WindsorHSRobotics/team-5115_2017-18/prints/gears/soldworks or fussion files/pinion rack mk1.SLDPRT

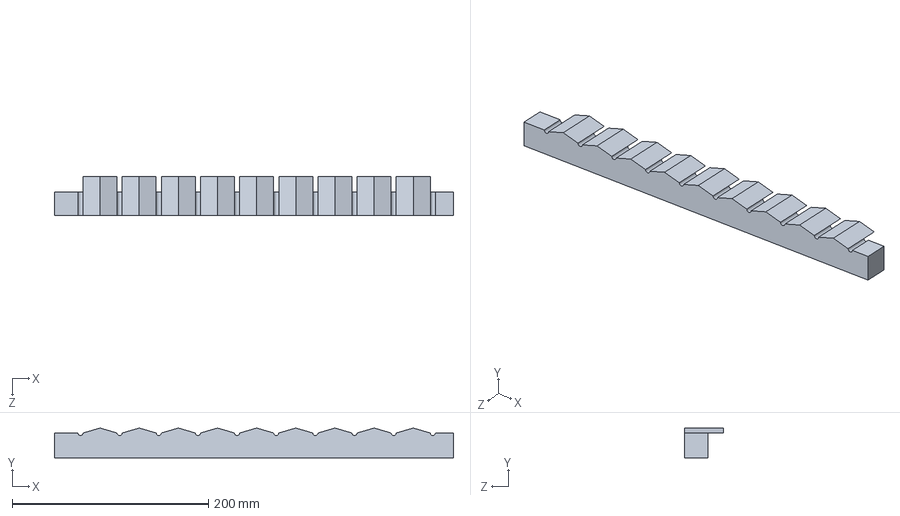
[picture p18: CAD file, 2018-01-17]
prints/gears/soldworks or fussion files/pinion rack mk1.SLDPRT
406.4 x 30.5 x 39.6 mm
