WindsorHSRobotics/team-5115_2017-18/prints/8020 brackets/stl files/90 degree 3 way corner bracket.stl

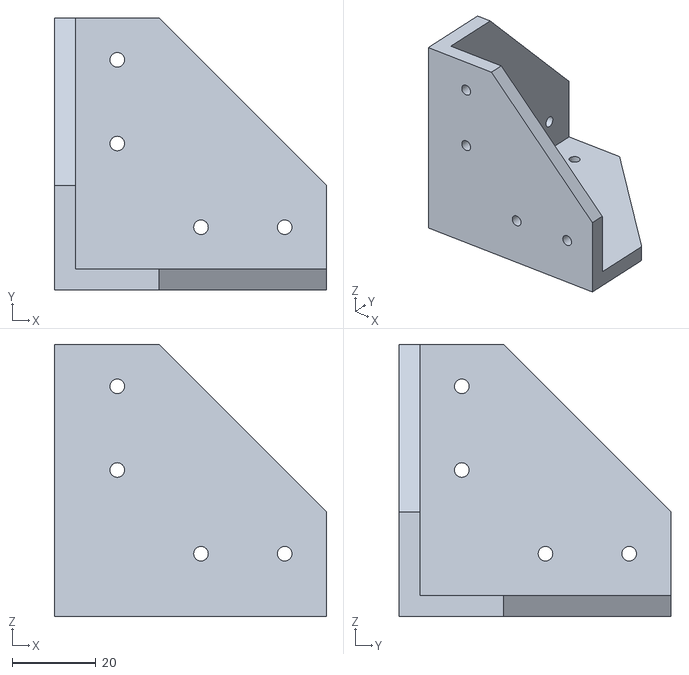
[picture p19: CAD file, 2017-10-06]
prints/8020 brackets/stl files/90 degree 3 way corner bracket.stl
65.0 x 65.0 x 65.0
