WindsorHSRobotics/team-5115_2017-18/prints/adapters/stl files/clawmk5.STL

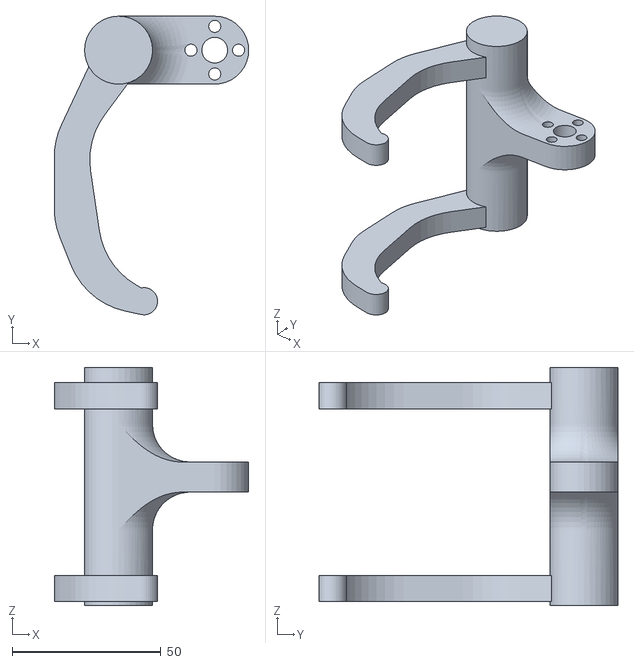
[picture p20: CAD file, 2018-01-09]
prints/adapters/stl files/clawmk5.STL
65.4 x 100.4 x 80.0
