WindsorHSRobotics/team-5115_2017-18/prints/gears/soldworks or fussion files/pin mk1.SLDPRT

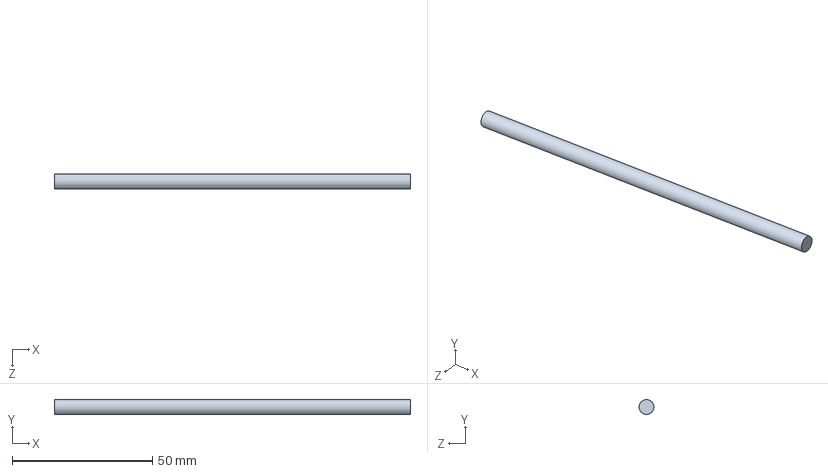
[picture p22: CAD file, 2018-01-17]
prints/gears/soldworks or fussion files/pin mk1.SLDPRT
127.0 x 5.33 x 5.33 mm
