WindsorHSRobotics/team-5115_2017-18/prints/gears/stl files/Gear_Rack_4inCircumference_2.222inLength.stl

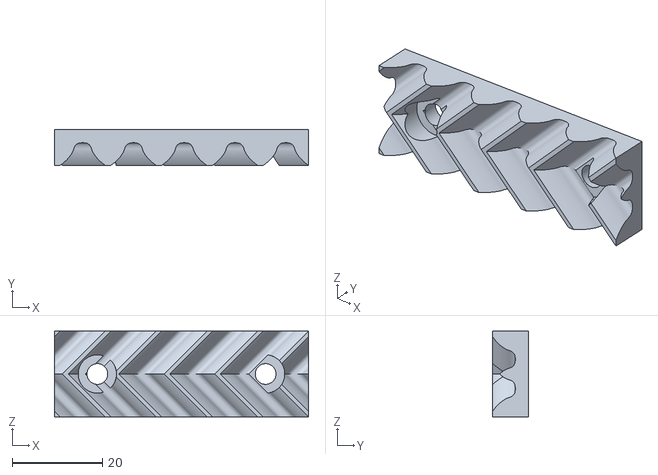
[picture p23: CAD file, 2017-12-08]
prints/gears/stl files/Gear_Rack_4inCircumference_2.222inLength.stl
56.4 x 7.94 x 19.1
