WindsorHSRobotics/team-5115_2017-18/prints/8020 brackets/stl files/90 degree joining plane.stl

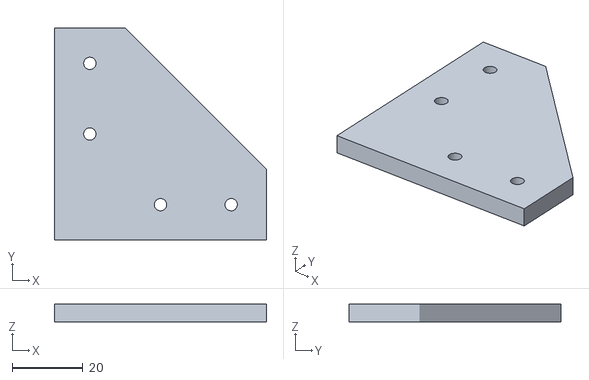
[picture p24: CAD file, 2017-10-06]
prints/8020 brackets/stl files/90 degree joining plane.stl
60.0 x 60.0 x 5.00
