WindsorHSRobotics/team-5115_2017-18/prints/adapters/sketchup of fusion files/4in mechanum adapter.SLDPRT

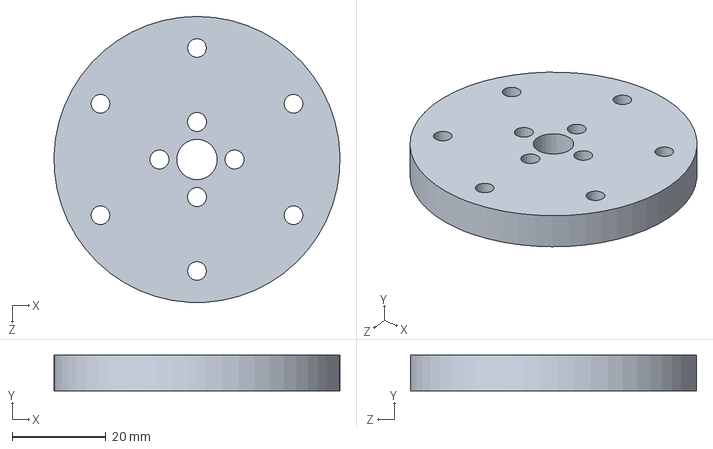
[picture p25: CAD file, 2018-01-30]
prints/adapters/sketchup of fusion files/4in mechanum adapter.SLDPRT
60.9 x 7.62 x 61.0 mm
