WindsorHSRobotics/team-5115_2017-18/prints/adapters/stl files/core device strain relief 1.STL

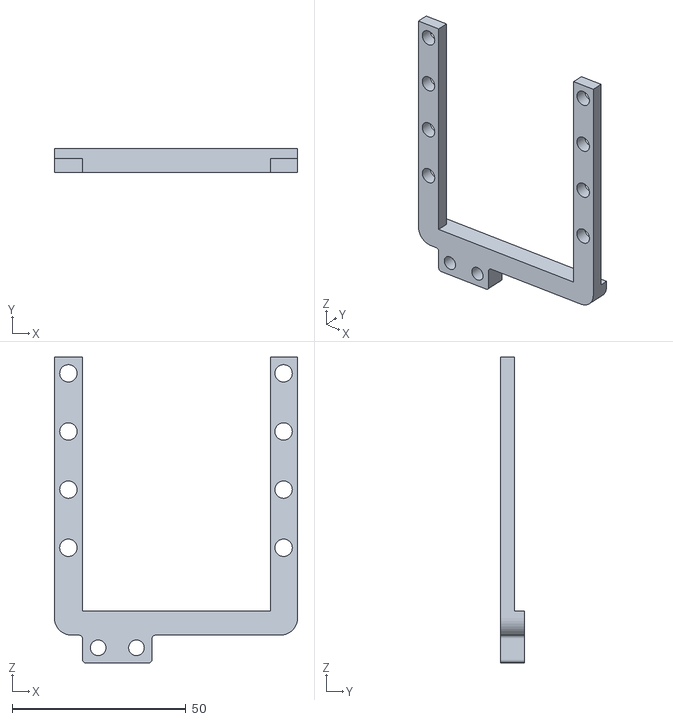
[picture p26: CAD file, 2017-12-21]
prints/adapters/stl files/core device strain relief 1.STL
70.0 x 6.80 x 88.0
