WindsorHSRobotics/team-5115_2017-18/prints/connectors/hinges/sti files/hinge pin.stl

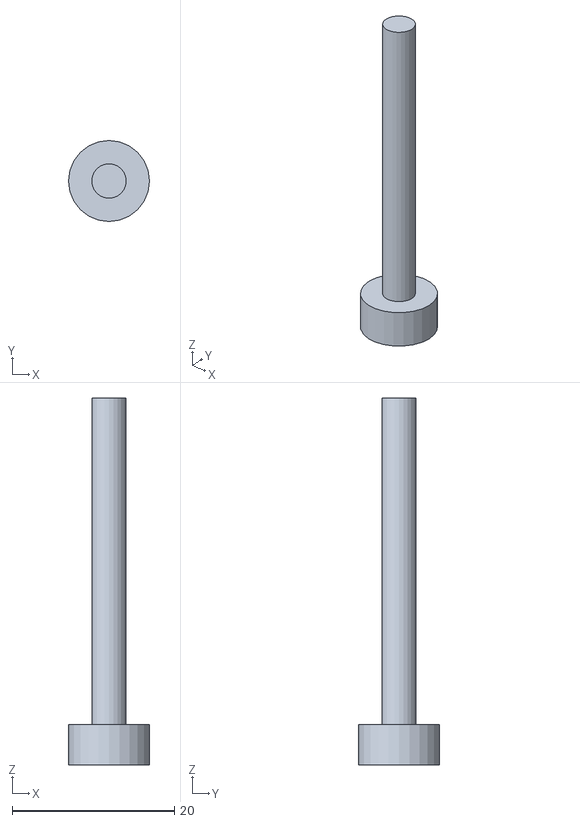
[picture p27: CAD file, 2017-10-03]
prints/connectors/hinges/sti files/hinge pin.stl
10.0 x 10.0 x 45.3
