WindsorHSRobotics/team-5115_2017-18/prints/gears/stl files/GearPinion_4inCircumference.stl

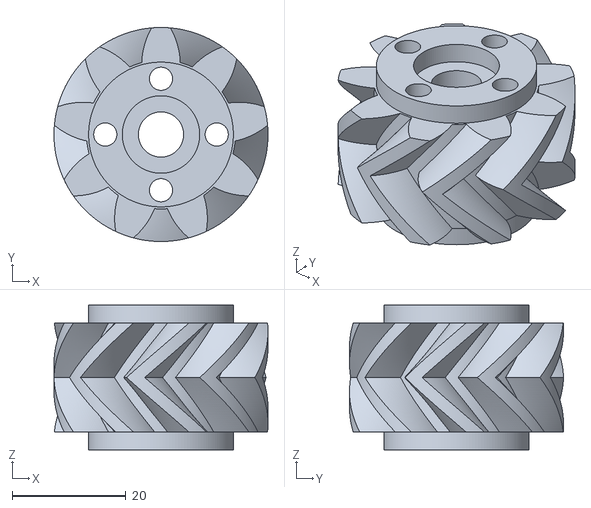
[picture p28: CAD file, 2017-12-08]
prints/gears/stl files/GearPinion_4inCircumference.stl
37.5 x 37.5 x 25.4
