WindsorHSRobotics/team-5115_2017-18/prints/8020 brackets/stl files/t joining plate.stl

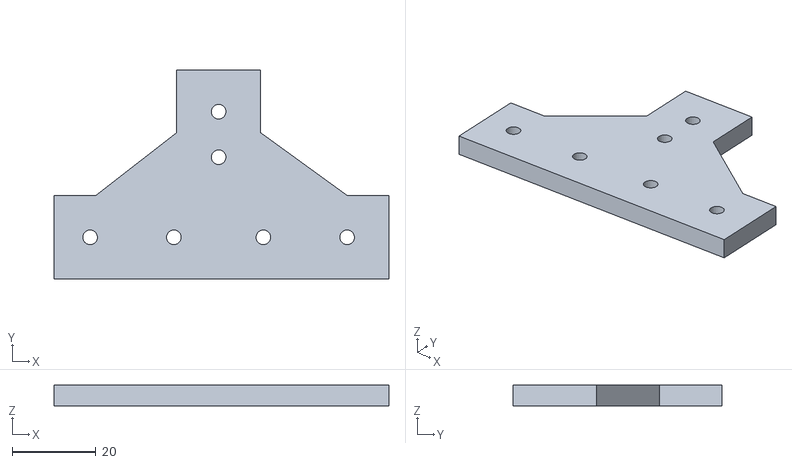
[picture p29: CAD file, 2017-10-06]
prints/8020 brackets/stl files/t joining plate.stl
80.0 x 50.0 x 5.00
