WindsorHSRobotics/team-5115_2017-18/prints/adapters/sketchup of fusion files/4in mechanum outside logo.SLDPRT

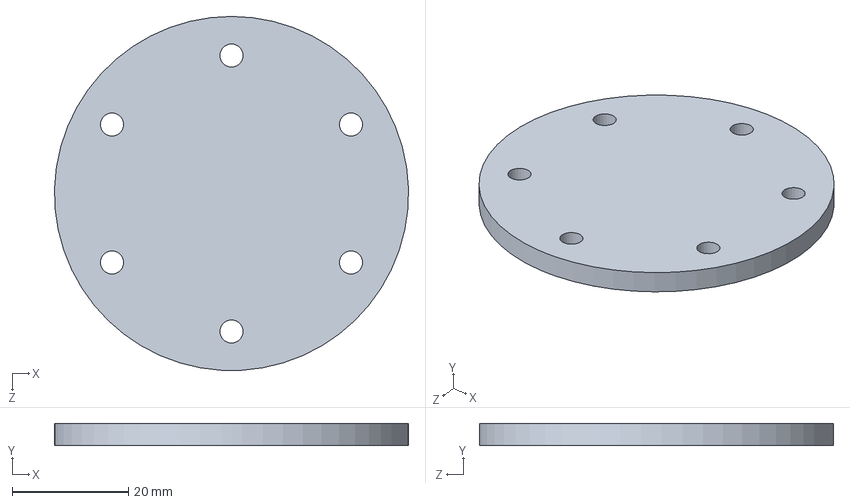
[picture p30: CAD file, 2018-01-09]
prints/adapters/sketchup of fusion files/4in mechanum outside logo.SLDPRT
60.9 x 3.81 x 61.0 mm
