WindsorHSRobotics/team-5115_2017-18/prints/adapters/stl files/brake servo adapter mk1.STL

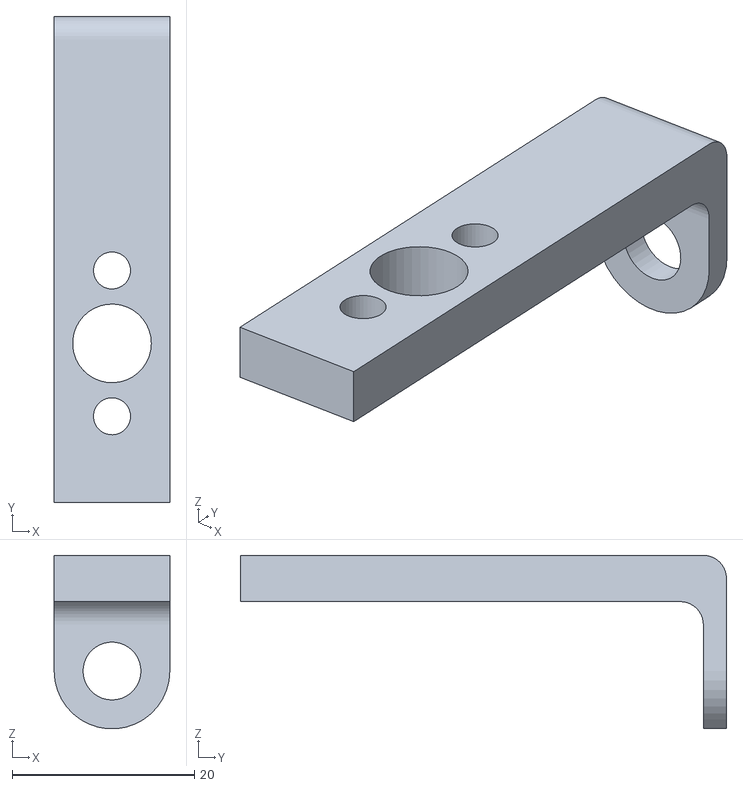
[picture p31: CAD file, 2017-12-20]
prints/adapters/stl files/brake servo adapter mk1.STL
12.7 x 53.3 x 19.0
