WindsorHSRobotics/team-5115_2017-18/prints/connectors/hinges/sti files/hinge 2 a.stl

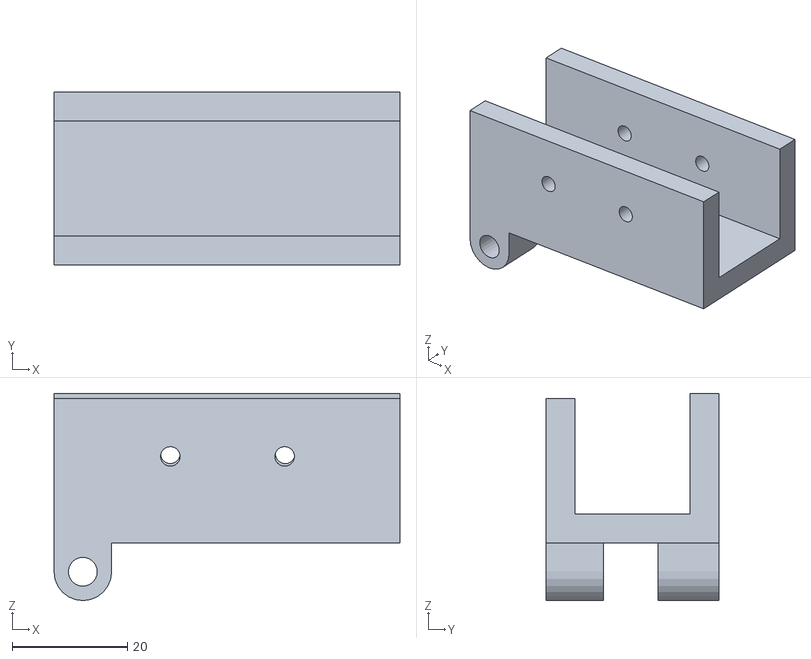
[picture p32: CAD file, 2017-10-03]
prints/connectors/hinges/sti files/hinge 2 a.stl
60.0 x 30.0 x 35.9
