WindsorHSRobotics/team-5115_2017-18/prints/gears/soldworks or fussion files/GenevaDriveWheel10inmkl1.SLDPRT

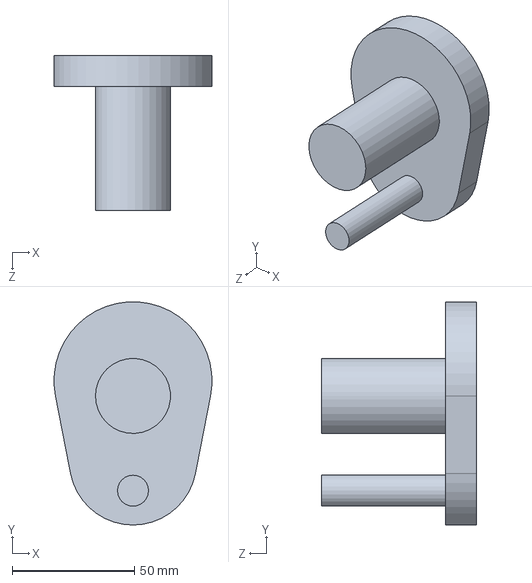
[picture p33: CAD file, 2017-12-14]
prints/gears/soldworks or fussion files/GenevaDriveWheel10inmkl1.SLDPRT
64.6 x 91.3 x 63.5 mm
