WindsorHSRobotics/team-5115_2017-18/prints/gears/stl files/Gear_Rack_4inCircumference_5.777inLength.stl

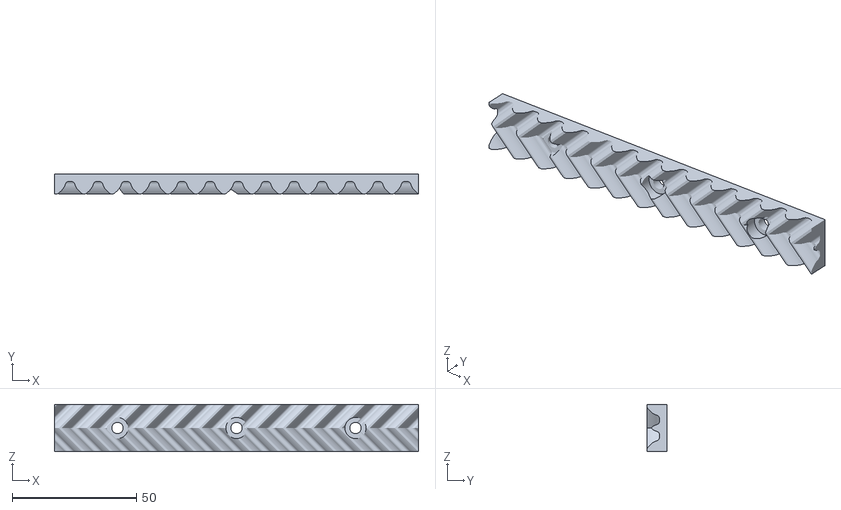
[picture p34: CAD file, 2017-12-08]
prints/gears/stl files/Gear_Rack_4inCircumference_5.777inLength.stl
146.8 x 7.94 x 19.1
