WindsorHSRobotics/team-5115_2017-18/prints/adapters/stl files/brakemountmk1.SLDPRT

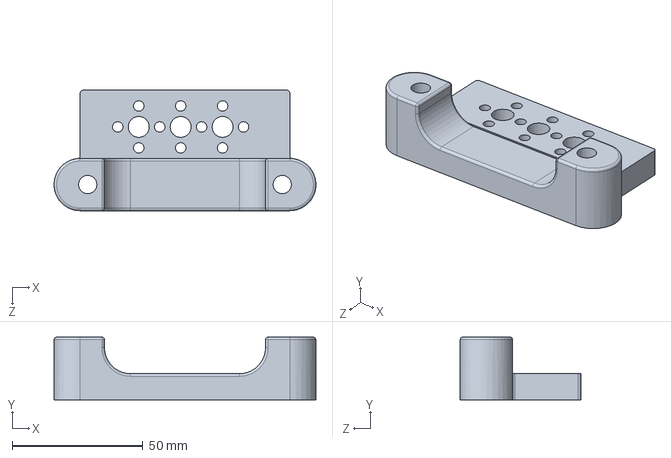
[picture p35: CAD file, 2017-12-14]
prints/adapters/stl files/brakemountmk1.SLDPRT
100.0 x 24.0 x 46.0 mm
