WindsorHSRobotics/team-5115_2017-18/prints/connectors/hinges/sti files/hinge 2 linkage.stl

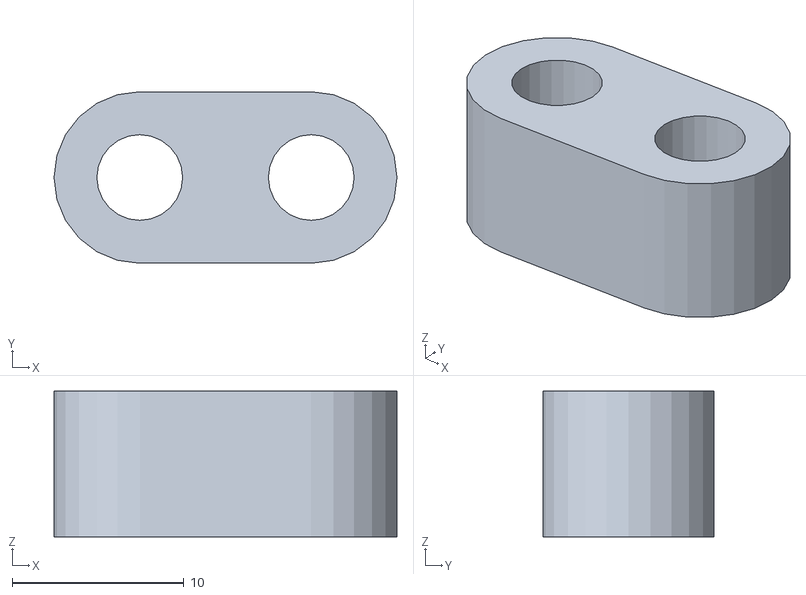
[picture p36: CAD file, 2017-10-03]
prints/connectors/hinges/sti files/hinge 2 linkage.stl
20.0 x 10.0 x 8.50
