WindsorHSRobotics/team-5115_2017-18/prints/gears/soldworks or fussion files/GenevaWheel10inmk1.SLDPRT

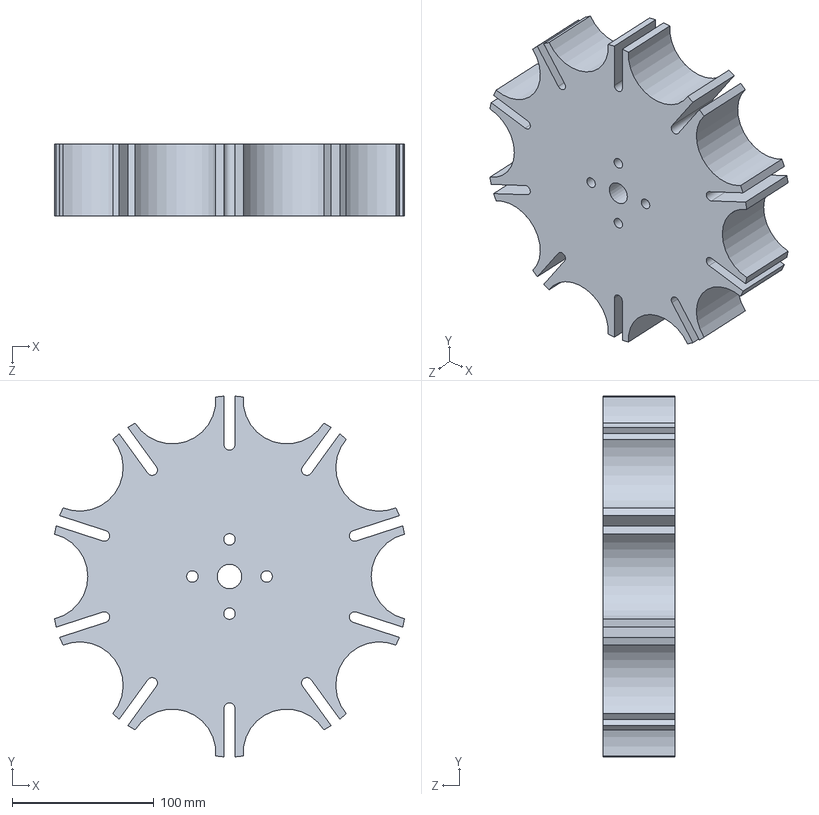
[picture p37: CAD file, 2017-12-14]
prints/gears/soldworks or fussion files/GenevaWheel10inmk1.SLDPRT
246.9 x 254.5 x 50.8 mm
