WindsorHSRobotics/team-5115_2017-18/prints/gears/stl files/Gear_Rack_4inCircumference_4inLength.stl

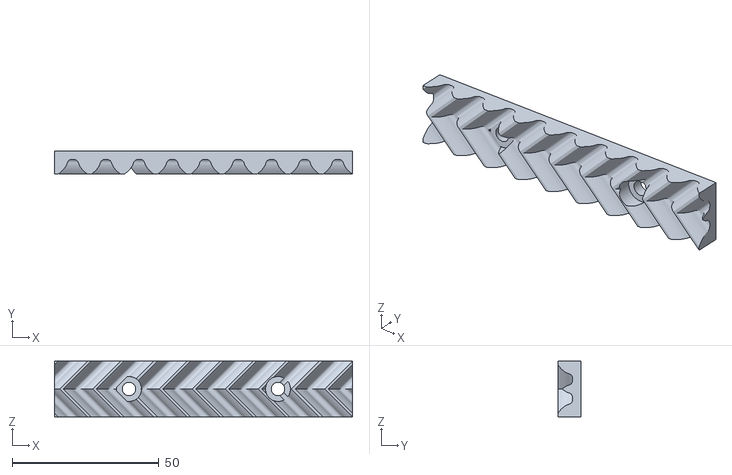
[picture p38: CAD file, 2017-12-08]
prints/gears/stl files/Gear_Rack_4inCircumference_4inLength.stl
101.6 x 7.94 x 19.1
