WindsorHSRobotics/team-5115_2017-18/prints/adapters/stl files/rotorhummk1.STL

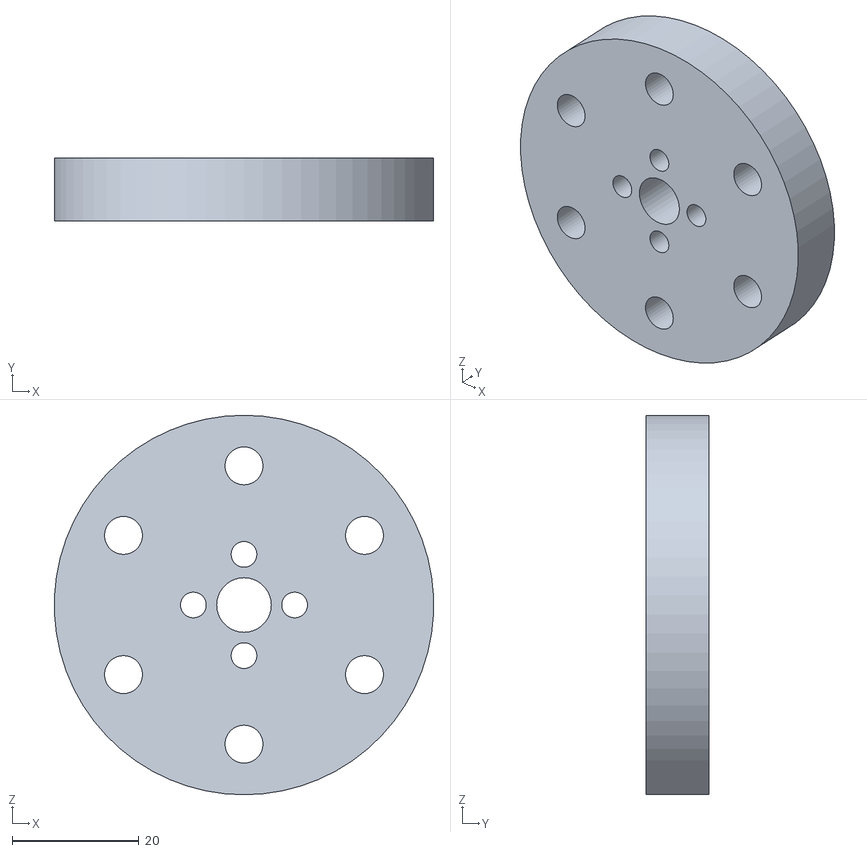
[picture p40: CAD file, 2017-12-14]
prints/adapters/stl files/rotorhummk1.STL
59.9 x 10.0 x 60.0
