WindsorHSRobotics/team-5115_2017-18/prints/gears/stl files/rack_herringbone.stl

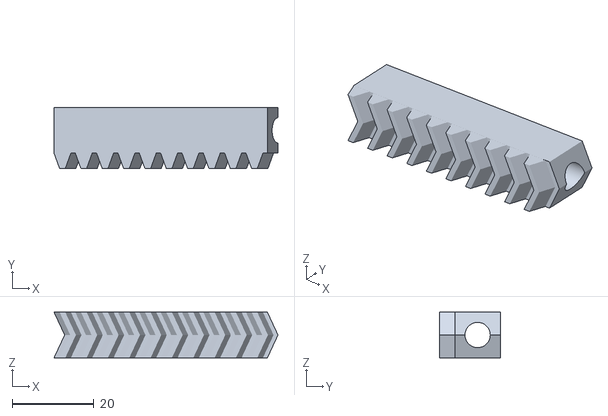
[picture p41: CAD file, 2017-12-08]
prints/gears/stl files/rack_herringbone.stl
55.0 x 14.9 x 11.3
