WindsorHSRobotics/team-5115_2017-18/prints/adapters/stl files/drawerslidetopmk2.STL

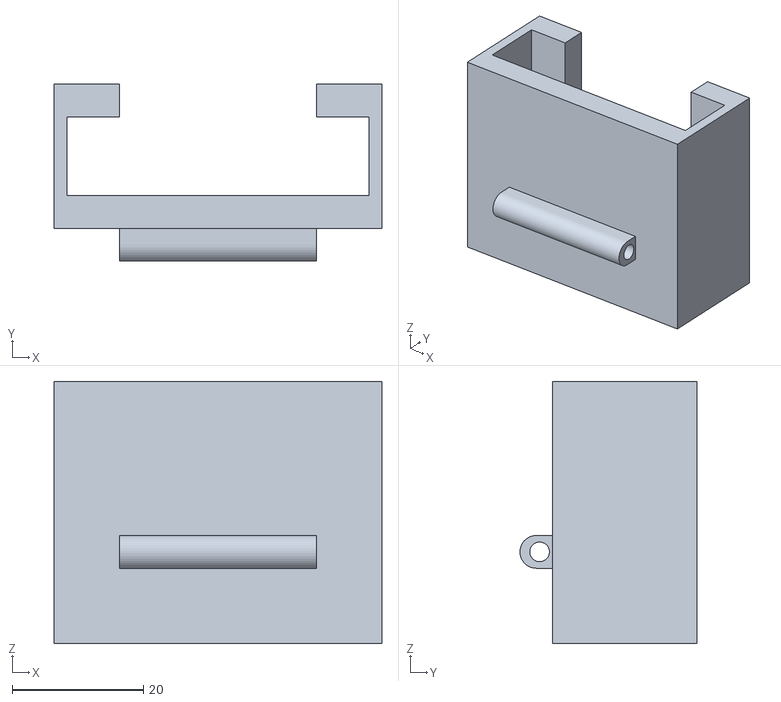
[picture p42: CAD file, 2017-12-08]
prints/adapters/stl files/drawerslidetopmk2.STL
50.0 x 27.0 x 40.0
