WindsorHSRobotics/team-5115_2017-18/prints/adapters/stl files/drawerslidetopmk3.STL

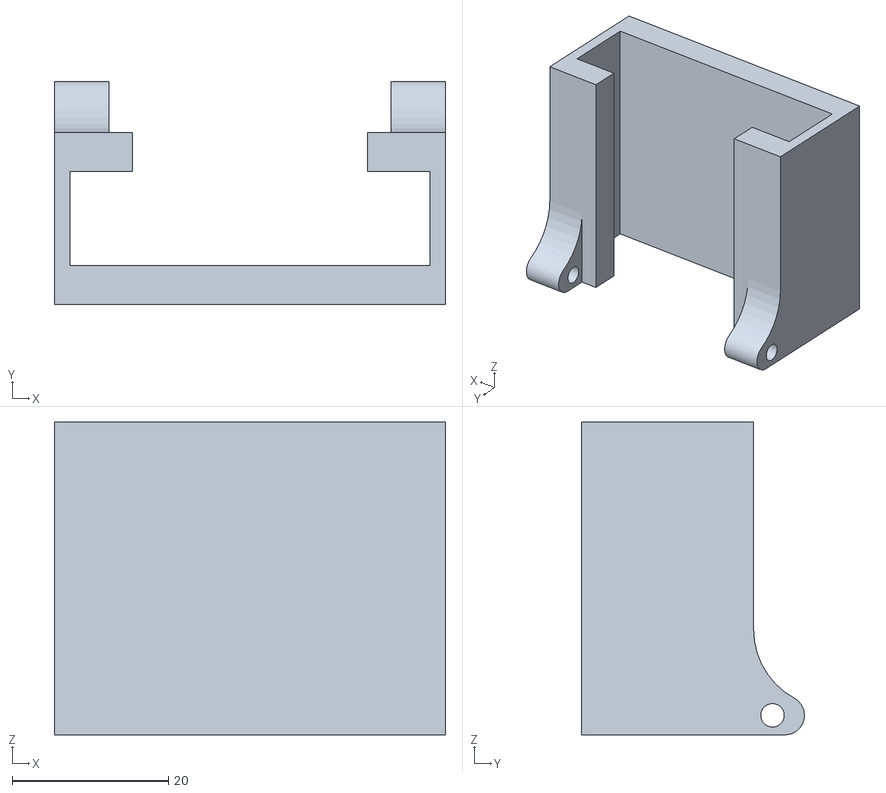
[picture p44: CAD file, 2017-12-08]
prints/adapters/stl files/drawerslidetopmk3.STL
50.0 x 28.5 x 40.0
