WindsorHSRobotics/team-5115_2017-18/prints/gears/stl files/rack_simple.Stl

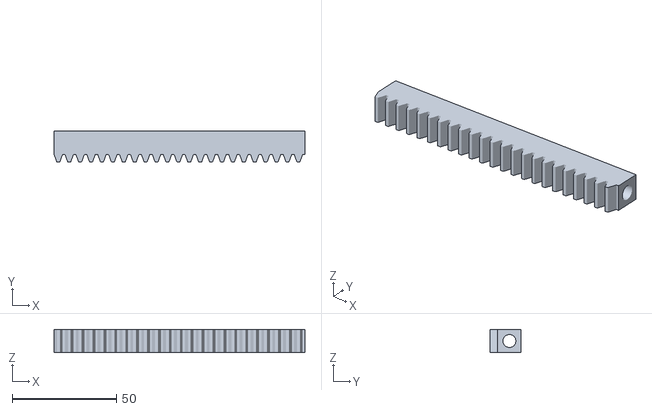
[picture p45: CAD file, 2017-12-08]
prints/gears/stl files/rack_simple.Stl
120.4 x 14.9 x 11.2
