WindsorHSRobotics/team-5115_2017-18/prints/adapters/stl files/clawmk1.STL

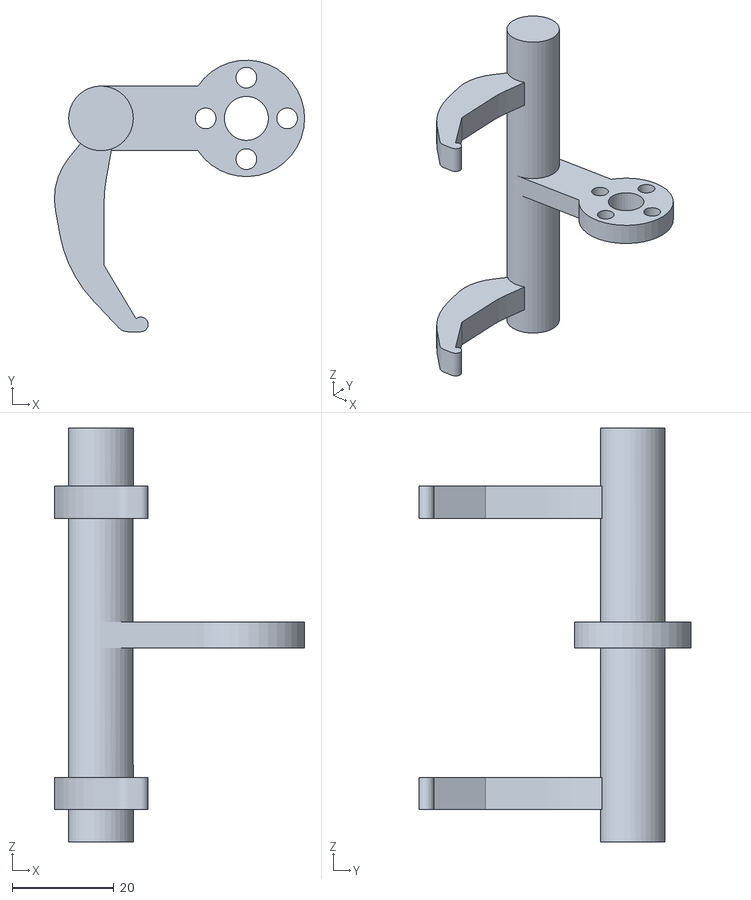
[picture p46: CAD file, 2017-11-27]
prints/adapters/stl files/clawmk1.STL
49.1 x 53.3 x 81.3
