WindsorHSRobotics/team-5115_2017-18/prints/gears/stl files/Gear_Rack_4inCircumference_8inLength.stl

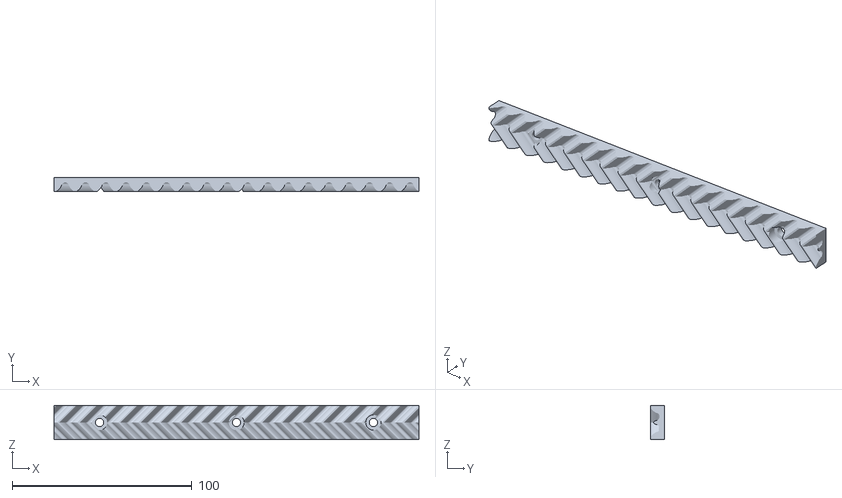
[picture p47: CAD file, 2017-12-08]
prints/gears/stl files/Gear_Rack_4inCircumference_8inLength.stl
203.2 x 7.94 x 19.1
