WindsorHSRobotics/team-5115_2017-18/prints/adapters/sketchup of fusion files/drawerslidebottom.SLDPRT

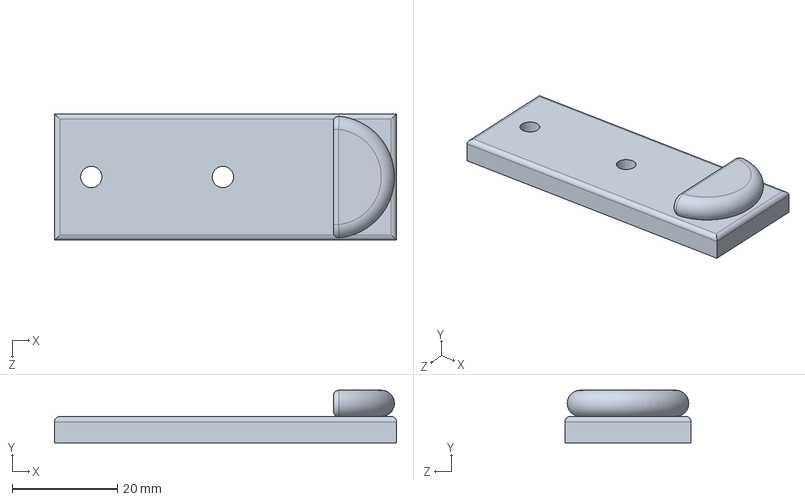
[picture p48: CAD file, 2017-11-27]
prints/adapters/sketchup of fusion files/drawerslidebottom.SLDPRT
65.0 x 10.0 x 24.0 mm
