WindsorHSRobotics/team-5115_2017-18/prints/adapters/stl files/drawerslidetop.STL

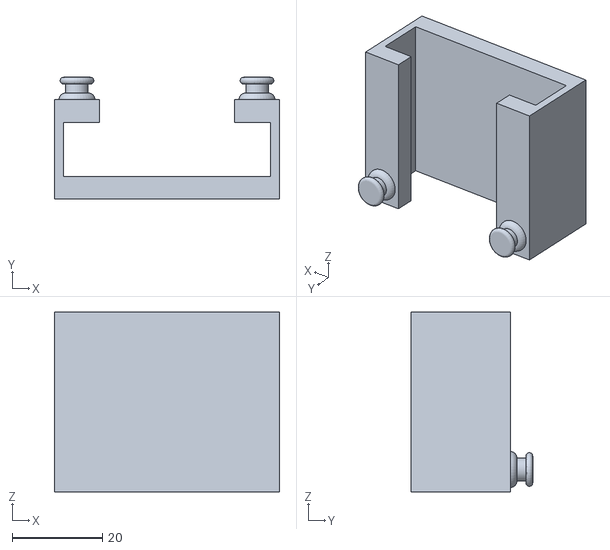
[picture p49: CAD file, 2017-11-02]
prints/adapters/stl files/drawerslidetop.STL
50.0 x 27.0 x 40.0
