WindsorHSRobotics/team-5115_2017-18/prints/adapters/stl files/liniar slide.stl

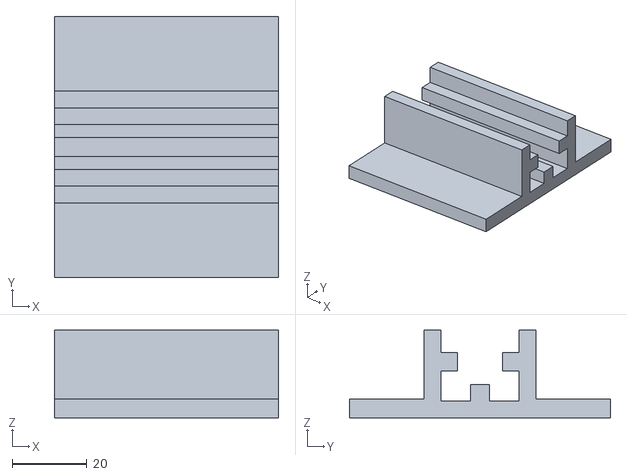
[picture p50: CAD file, 2017-11-02]
prints/adapters/stl files/liniar slide.stl
60.0 x 70.0 x 23.5
