WindsorHSRobotics/team-5115_2017-18/prints/adapters/stl files/mecanum_axlehub_adapter.stl

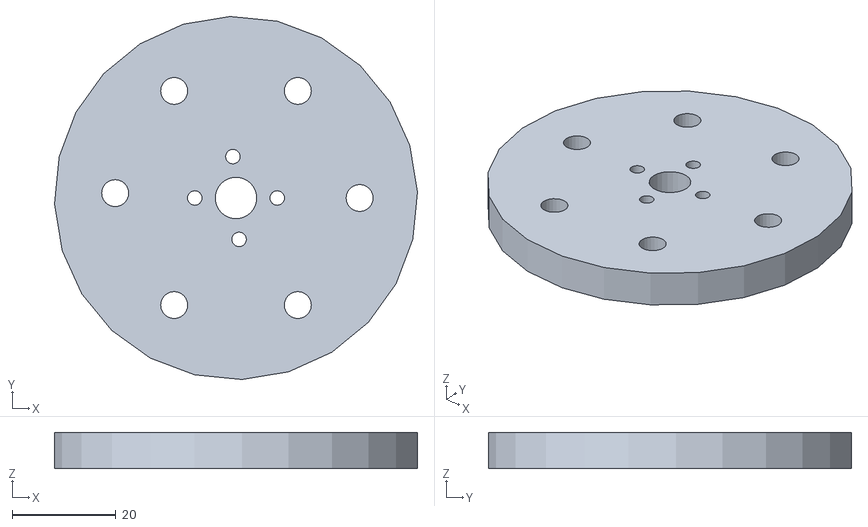
[picture p51: CAD file, 2017-10-03]
prints/adapters/stl files/mecanum_axlehub_adapter.stl
70.0 x 70.0 x 7.00
