WindsorHSRobotics/team-5115_2017-18/ftc_app-master/FtcRobotController/src/main/java/com/qualcomm/ftcrobotcontroller/opmodes/IDontCare.java

/*package com.qualcomm.ftcrobotcontroller.opmodes;

import com.qualcomm.robotcore.hardware.DcMotor;
import com.qualcomm.robotcore.eventloop.opmode.OpMode;
import com.qualcomm.robotcore.hardware.HardwareMap;
import com.qualcomm.robotcore.hardware.Servo;
import com.qualcomm.robotcore.util.Range;

/**
 * Created by domma on 1/20/2017.
 */
/*public class teli10736 extends OpMode {

    DcMotor motorLeft;
    DcMotor motorRight;
    Servo arm;

    final static double ARM_MIN_RANGE = 0.01;
    final static double ARM_MAX_RANGE = 0.99;

    // position of the arm servo.
    double armPosition;

    // amount to change the arm servo position.
    double armDelta = 0.05;


    public void runOpMode() throws InterruptedException {
        motorLeft = hardwareMap.dcMotor.get("motorLeft");
        motorRight = hardwareMap.dcMotor.get("motorRight");
        motorRight.setDirection(DcMotor.Direction.REVERSE);
        arm = hardwareMap.servo.get("servoDoor");

        armPosition = 0.2;
    }
}
*/
