WindsorHSRobotics/team-5115_2017-18/ftc_app-master/FtcRobotController/src/main/java/com/qualcomm/ftcrobotcontroller/opmodes/ExampleTeleopTankMode.java

package com.qualcomm.ftcrobotcontroller.opmodes;

import com.qualcomm.robotcore.eventloop.opmode.OpMode;
import com.qualcomm.robotcore.hardware.DcMotor;


public class ExampleTeleopTankMode extends OpMode {

    DcMotor leftMotor;
    DcMotor rightMotor;

    @Override
    public void init() {
        //get references to the motors from the hardware map
        leftMotor = hardwareMap.dcMotor.get("left_drive");
        rightMotor = hardwareMap.dcMotor.get("right_drive");

        //reverse the right motor
        rightMotor.setDirection(DcMotor.Direction.REVERSE);
        leftMotor.setDirection(DcMotor.Direction.FORWARD);
    }

    @Override
    public void loop() {
        //get the values from the gamepads
        //note: pushing the stick all the way up returns -1,
        // so we need to reverse the values
        float leftY = -gamepad1.left_stick_y;
        float rightY = -gamepad1.right_stick_y;

        //set the power of the motors with the gamepad values
        leftMotor.setPower(leftY);
        rightMotor.setPower(rightY);
    }
}
